ChemaFuji/CatPrinter/imprimir/carro-y_new3.stl

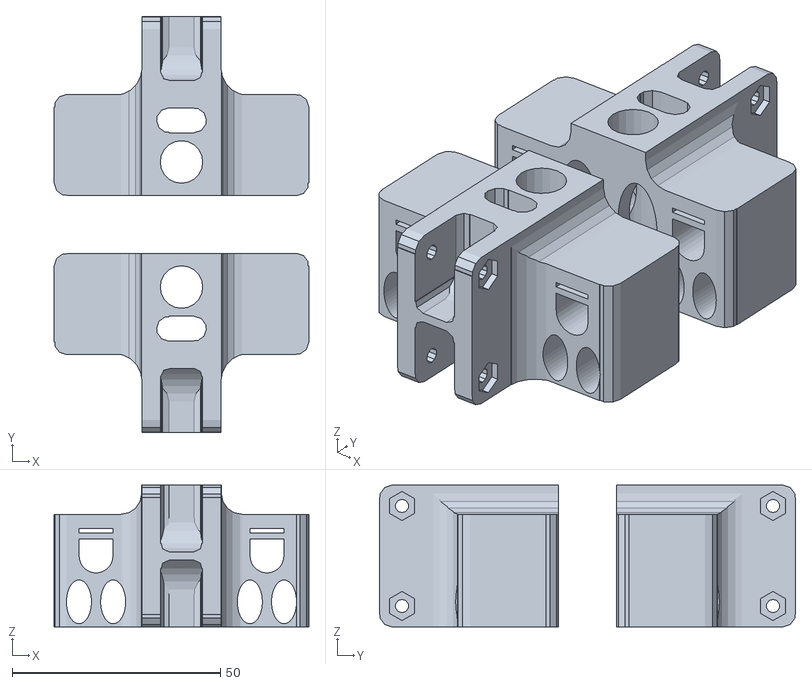
[picture p21: CAD file, 2013-06-23]
imprimir/carro-y_new3.stl
61.1 x 99.8 x 34.0
