ChemaFuji/CatPrinter/imprimir/carro-y_new2_brim.stl

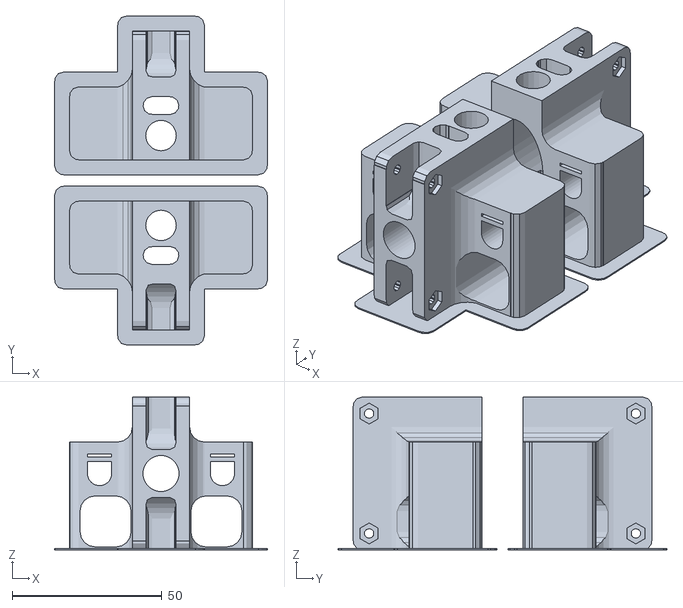
[picture p22: CAD file, 2013-06-23]
imprimir/carro-y_new2_brim.stl
71.1 x 109.8 x 51.0
