ChemaFuji/CatPrinter/imprimir/carro-y_new_brim.stl

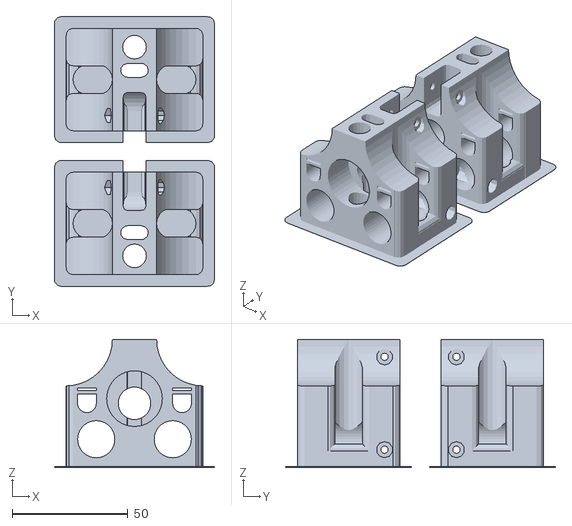
[picture p23: CAD file, 2013-06-21]
imprimir/carro-y_new_brim.stl
69.1 x 116.4 x 55.2
