ChemaFuji/CatPrinter/imprimir/Z-axis_brim.stl

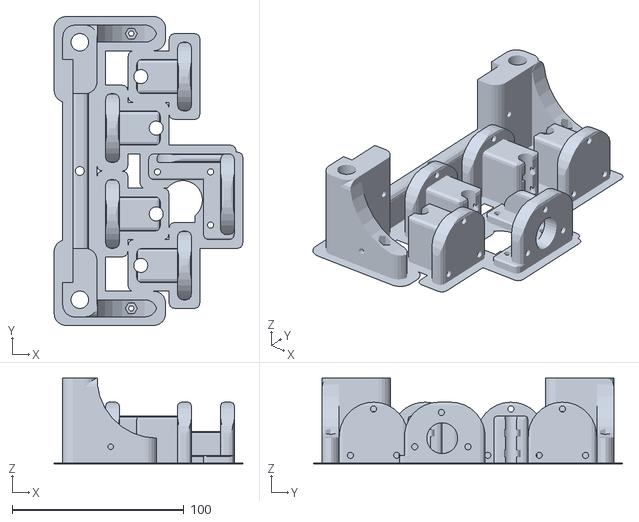
[picture p24: CAD file, 2013-06-21]
imprimir/Z-axis_brim.stl
110.0 x 180.0 x 50.0
