ChemaFuji/CatPrinter/imprimir/Z-axis.stl

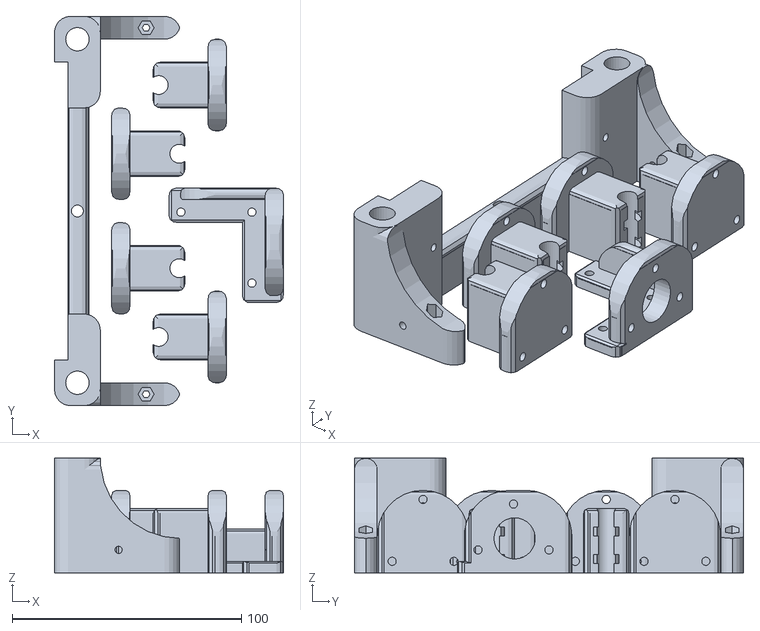
[picture p25: CAD file, 2013-06-21]
imprimir/Z-axis.stl
100.0 x 170.0 x 50.0
