ChemaFuji/CatPrinter/imprimir/y_end_motor_new.stl

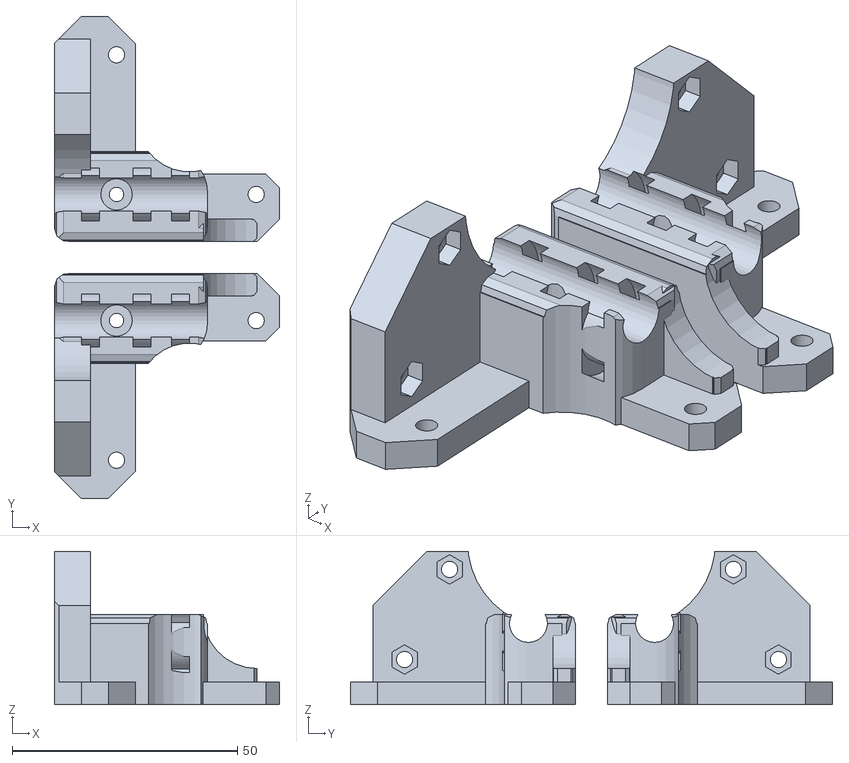
[picture p26: CAD file, 2013-06-19]
imprimir/y_end_motor_new.stl
50.0 x 107.0 x 34.0
