ChemaFuji/CatPrinter/imprimir/fijaciones carro-x.stl

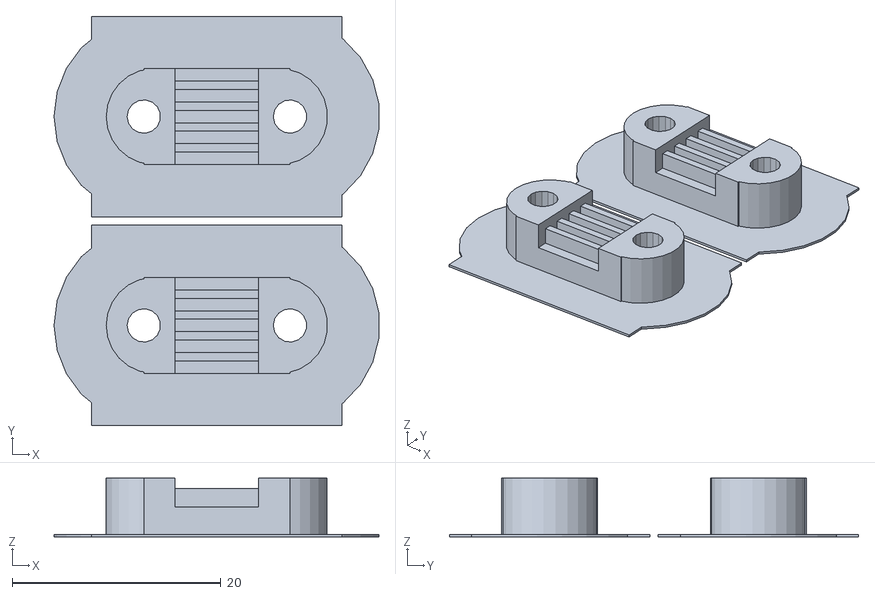
[picture p27: CAD file, 2013-06-15]
imprimir/fijaciones carro-x.stl
31.1 x 39.2 x 5.62
