ChemaFuji/CatPrinter/imprimir/carro-x_aligerado.stl

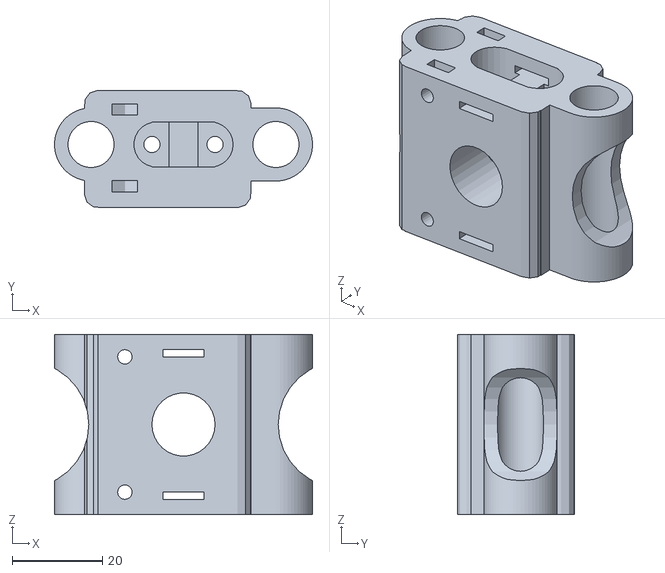
[picture p28: CAD file, 2013-06-10]
imprimir/carro-x_aligerado.stl
57.2 x 26.0 x 40.0
