ChemaFuji/CatPrinter/imprimir/carro-x_brim_aligerado.stl

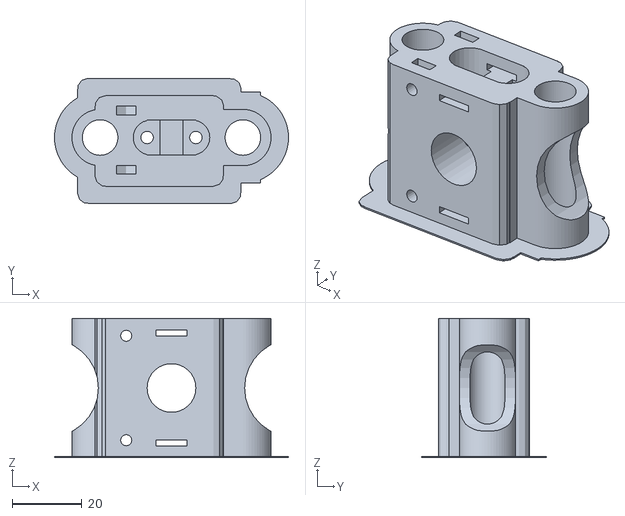
[picture p29: CAD file, 2013-06-10]
imprimir/carro-x_brim_aligerado.stl
67.2 x 36.0 x 40.0
