ChemaFuji/CatPrinter/imprimir/Y-end-motor.stl

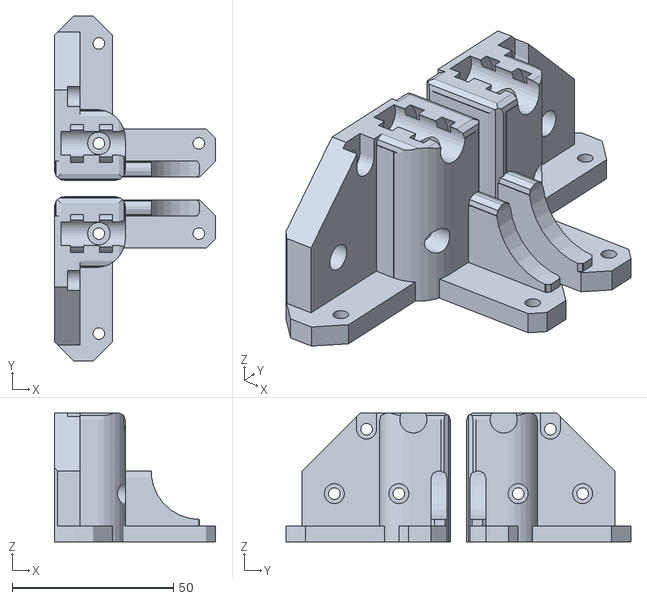
[picture p30: CAD file, 2013-06-08]
imprimir/Y-end-motor.stl
50.0 x 107.0 x 40.0
