ChemaFuji/CatPrinter/imprimir/y_end_idler.stl

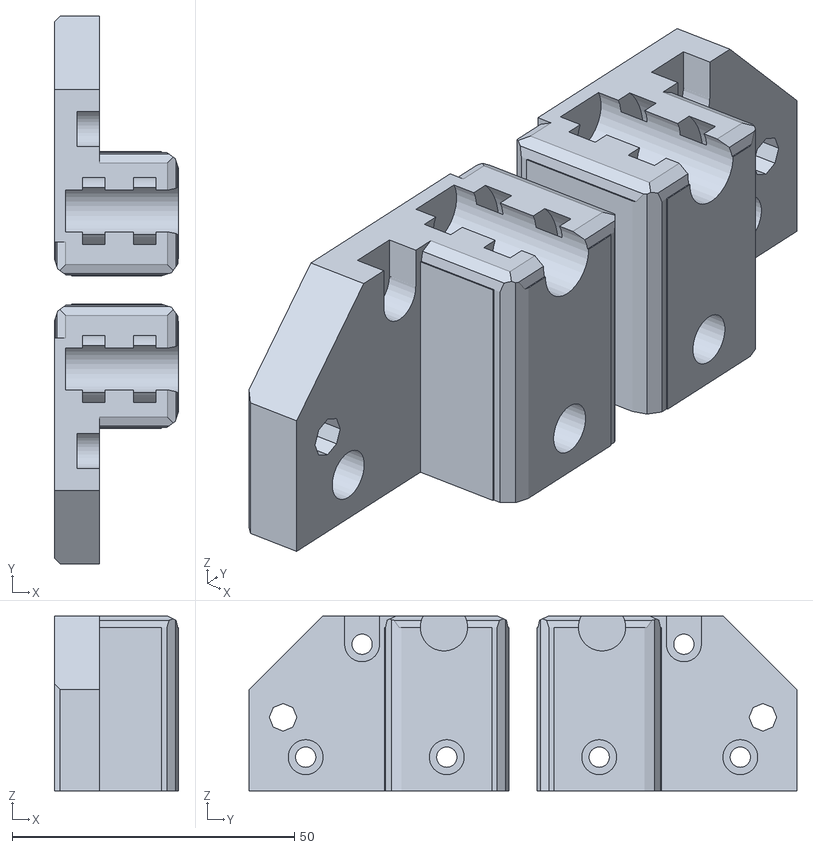
[picture p31: CAD file, 2013-06-08]
imprimir/y_end_idler.stl
22.0 x 97.0 x 31.0
