ChemaFuji/CatPrinter/imprimir/carro-y.stl

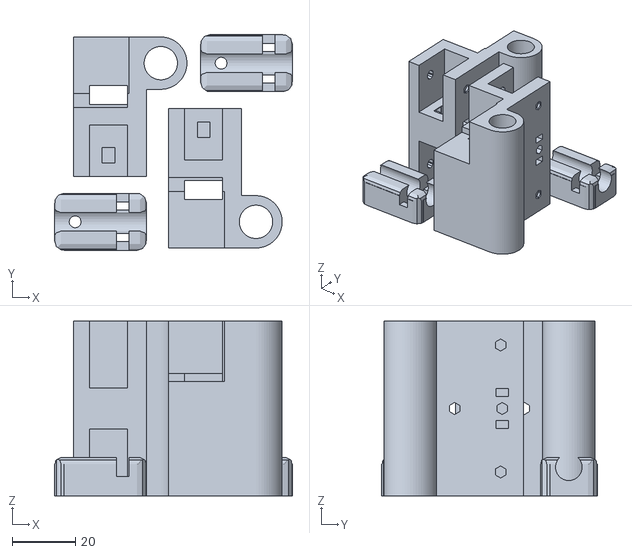
[picture p32: CAD file, 2013-06-08]
imprimir/carro-y.stl
75.0 x 68.0 x 55.0
